Synthetic-Bits/Audio-Synthesizer/Audio_Synthesizer_H533/Core/Inc/main.h

/**
 ******************************************************************************
 * @file           : main.h
 * @brief          : Header for main.c file.  This file contains the common
 *                   defines of the application.
 * @authors        : Adrian Sucahyo, Kenneth Gordon, Bryant Watson, Hayoung Im
 ******************************************************************************
 * @attention
 *
 * Copyright (c) 2025 STMicroelectronics.
 * All rights reserved.
 *
 * This software is licensed under terms that can be found in the LICENSE file
 * in the root directory of this software component.
 * If no LICENSE file comes with this software, it is provided AS-IS.
 *
 ******************************************************************************
 */

/* Define to prevent recursive inclusion -------------------------------------*/
#ifndef __MAIN_H
#define __MAIN_H

#ifdef __cplusplus
extern "C"
{
#endif

/* Includes ------------------------------------------------------------------*/
#include "stm32h5xx_hal.h"
#include "stm32h5xx_nucleo.h"
#include <stdio.h>

/* Private includes ----------------------------------------------------------*/

/* Exported types ------------------------------------------------------------*/

/* Exported constants --------------------------------------------------------*/

/* Exported macro ------------------------------------------------------------*/

/* Exported functions prototypes ---------------------------------------------*/
void Error_Handler(void);
void SystemClock_Config(void);
void MX_ICACHE_Init(void);

/* Private defines -----------------------------------------------------------*/
#define SWDIO_Pin GPIO_PIN_13
#define SWDIO_GPIO_Port GPIOA
#define SWCLK_Pin GPIO_PIN_14
#define SWCLK_GPIO_Port GPIOA
#define JTDI_Pin GPIO_PIN_15
#define JTDI_GPIO_Port GPIOA
#define SWO_Pin GPIO_PIN_3
#define SWO_GPIO_Port GPIOB

#ifdef __cplusplus
}
#endif

#endif /* __MAIN_H */
