Synthetic-Bits/Audio-Synthesizer/Audio_Synthesizer_F072/Inc/main.h

/**
 ******************************************************************************
 * @file           : main.h
 * @brief          : Main Header
 ******************************************************************************
 */

/* Includes ------------------------------------------------------------------*/

#pragma once
#include <stdint.h>

/* ========================================================================== */
/*                                                                            */
/*    RCC Clock Functions                                                     */
/*                                                                            */
/* ========================================================================== */

// GPIO
void HAL_RCC_GPIOA_CLK_Enable(void);
void HAL_RCC_GPIOB_CLK_Enable(void);
void HAL_RCC_GPIOC_CLK_Enable(void);

// Timer RCC Enables
void HAL_RCC_TIM2_CLK_Enable(void);
void HAL_RCC_TIM3_CLK_Enable(void);

// USART
void HAL_RCC_USART1_CLK_Enable(void);
void HAL_RCC_USART2_CLK_Enable(void);
void HAL_RCC_USART3_CLK_Enable(void);
void HAL_RCC_USART4_CLK_Enable(void);

/* ========================================================================== */
/*                                                                            */
/*    Checkpoint Functions                                                    */
/*                                                                            */
/* ========================================================================== */

/**
 * @brief This function runs the first checkpoint of the synthesizer project.
 * @param None
 * @retval None
 */
void checkpoint_1(void);

/**
 * @brief This function runs the second checkpoint of the synthesizer project.
 * @param None
 * @retval None
 */
void checkpoint_2(void);

/* ========================================================================== */
/*                                                                            */
/*    Misc Configuration Functions                                            */
/*                                                                            */
/* ========================================================================== */

/**
 * @brief This function configures the system clock on the microcontroller.
 * @param None
 * @retval None
 */
void SystemClock_Config(void);
