Synthetic-Bits/Audio-Synthesizer/Audio_Synthesizer_H533/Core/Src/rcc.c

/**
 ******************************************************************************
 * @file    rcc.c
 * @brief   RCC Timer Control Interface
 * @authors Adrian Sucahyo, Kenneth Gordon, Bryant Watson, and Hayoung Im
 ******************************************************************************
 * @attention
 *
 * Copyright (c) 2025 Synthetic Bits.
 * All rights reserved.
 *
 * This software is licensed under terms that can be found in the LICENSE file
 * in the root directory of this software component.
 * If no LICENSE file comes with this software, it is provided AS-IS.
 *
 ******************************************************************************
 */

/* Includes ------------------------------------------------------------------*/
#include "main.h"
#include "rcc.h"

/* Private includes ----------------------------------------------------------*/
#include <stdio.h>
#include <string.h>

#include "stm32h5xx.h"

/* Function Prototypes -------------------------------------------------------*/
void RCC_GPIOA_CLK_Enable(void);
void RCC_GPIOB_CLK_Enable(void);
void RCC_GPIOC_CLK_Enable(void);

void RCC_TIM2_CLK_Enable(void);
void RCC_TIM3_CLK_Enable(void);
void RCC_TIM4_CLK_Enable(void);

void RCC_DAC1_CLK_Enable(void);

void RCC_USART1_CLK_Enable(void);
void RCC_USART3_CLK_Enable(void);

/* ========================================================================== */
/*                                                                            */
/*    Control Functions                                                       */
/*                                                                            */
/* ========================================================================== */

/**
 * @brief Enable the GPIOA Clock using the RCC.
 */
void RCC_GPIOA_CLK_Enable()
{
    RCC->AHB2ENR |= RCC_AHB2ENR_GPIOAEN;
}

/**
 * @brief Enable the GPIOB Clock using the RCC.
 */
void RCC_GPIOB_CLK_Enable()
{
    RCC->AHB2ENR |= RCC_AHB2ENR_GPIOBEN;
}

/**
 * @brief Enable the GPIOC Clock using the RCC.
 */
void RCC_GPIOC_CLK_Enable()
{
    RCC->AHB2ENR |= RCC_AHB2ENR_GPIOCEN;
}

/**
 * @brief Enable the RCC Clock for TIM2
 */
void RCC_TIM2_CLK_Enable()
{
    RCC->APB1LENR |= RCC_APB1LENR_TIM2EN;
}

/**
 * @brief Enable the RCC Clock for TIM3
 */
void RCC_TIM3_CLK_Enable()
{
    RCC->APB1LENR |= RCC_APB1LENR_TIM3EN;
}

/**
 * @brief Enable the RCC Clock for TIM4
 */
void RCC_TIM4_CLK_Enable()
{
    RCC->APB1LENR |= RCC_APB1LENR_TIM4EN;
}

/**
 * @brief Enable the RCC Clock for TIM4
 */
void RCC_DAC1_CLK_Enable()
{
    RCC->AHB2ENR |= RCC_AHB2ENR_DAC1EN;
}

/**
 * @brief Enable the RCC Clock for USART1
 */
void RCC_USART1_CLK_Enable()
{
    RCC->APB2ENR |= RCC_APB2ENR_USART1EN;
}

/**
 * @brief Enable the RCC Clock for USART3
 */
void RCC_USART3_CLK_Enable()
{
    RCC->APB1LENR |= RCC_APB1LENR_USART3EN;
}
