Synthetic-Bits/Audio-Synthesizer/Audio_Synthesizer_F072/Inc/gpio.h

/**
 ******************************************************************************
 * @file           : gpio.h
 * @brief          : GPIO Interface Header
 ******************************************************************************
 */

/* Includes ------------------------------------------------------------------*/

#include "pins.h"

/* ========================================================================== */
/*                                                                            */
/*    Definitions                                                             */
/*                                                                            */
/* ========================================================================== */

#ifndef _GPIO_H_
#define _GPIO_H_

/* ========================================================================== */
/*                                                                            */
/*    Initialization Functions                                                */
/*                                                                            */
/* ========================================================================== */

/**
 * @brief Function that initializes the LEDs on the microcontroller.
 * @param None.
 * @retval None.
 */
void initializeLEDs();

#endif /* _GPIO_H_ */
